Kagami-1/AudioMorph/Images/0.96-inch-OLED-display-1-1536x1536.jpg

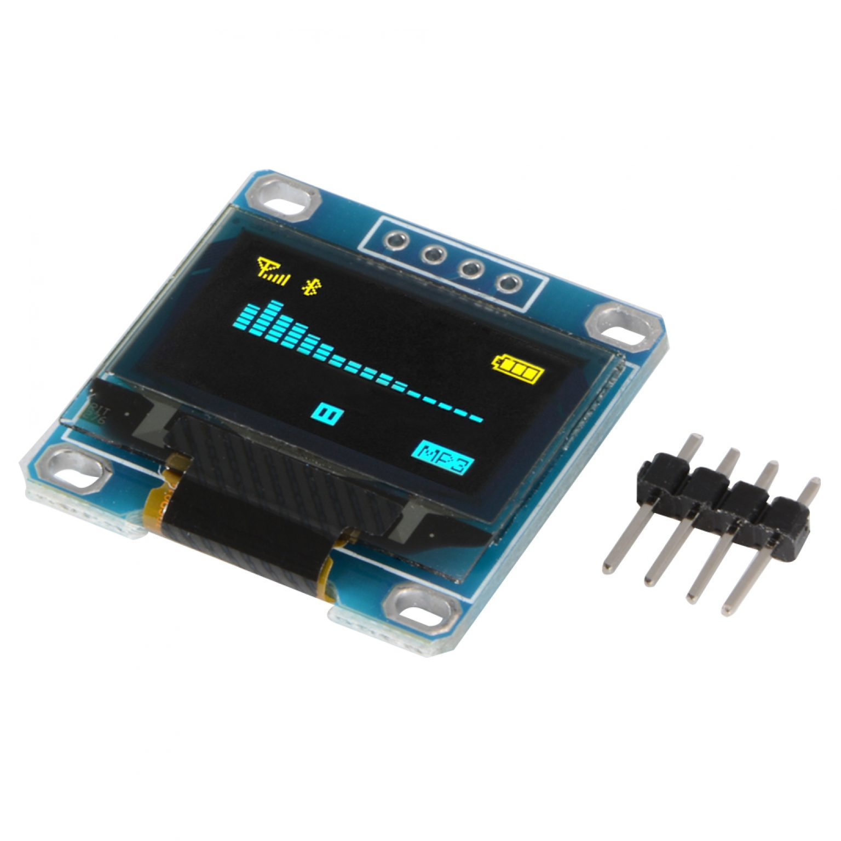
Images/0.96-inch-OLED-display-1-1536x1536.jpg
