Kagami-1/AudioMorph/Images/467a1c06-c707-43bd-9dd6-f2bde50086d6_1.46be4bbbeaa72e5d1ce6fceb8eb4fa7a.webp

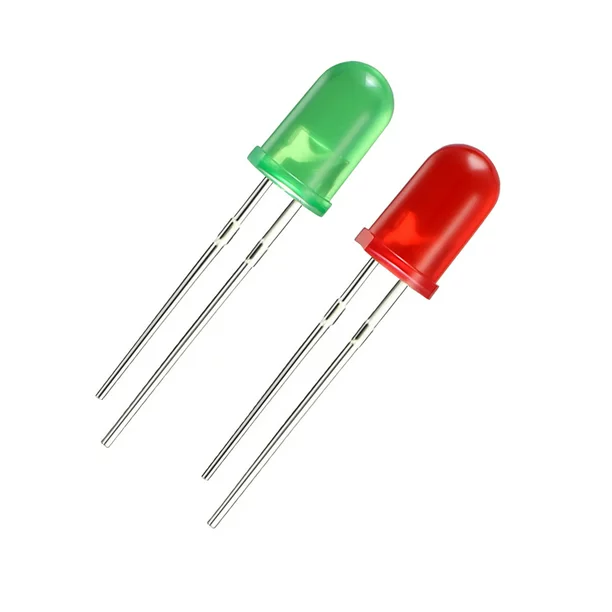
Images/467a1c06-c707-43bd-9dd6-f2bde50086d6_1.46be4bbbeaa72e5d1ce6fceb8eb4fa7a.webp
