Kagami-1/AudioMorph/Images/breadboard.jpg

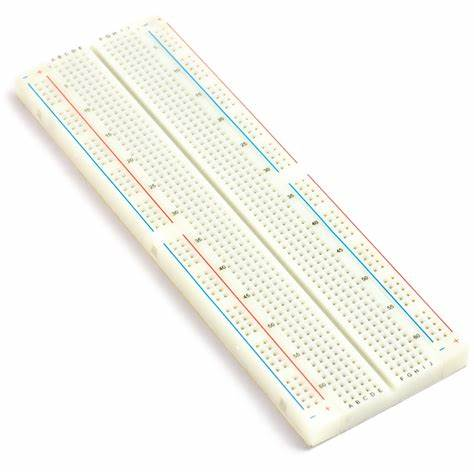
Images/breadboard.jpg
