Kagami-1/AudioMorph/Images/ezgif-1-566e2a0541.gif

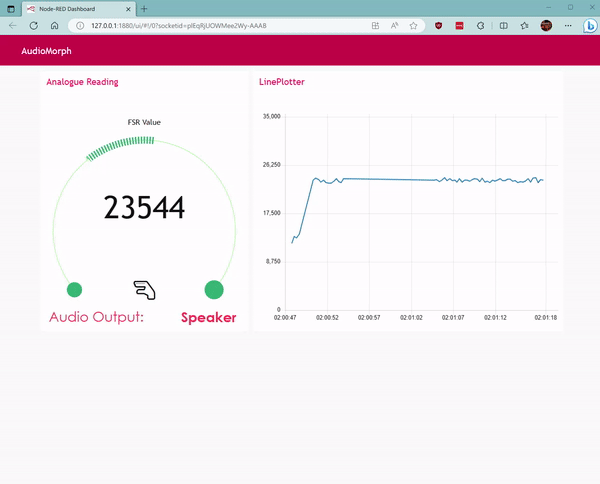
Images/ezgif-1-566e2a0541.gif
