Kagami-1/AudioMorph/Images/New folder/Screenshot 2023-07-06 210006.png

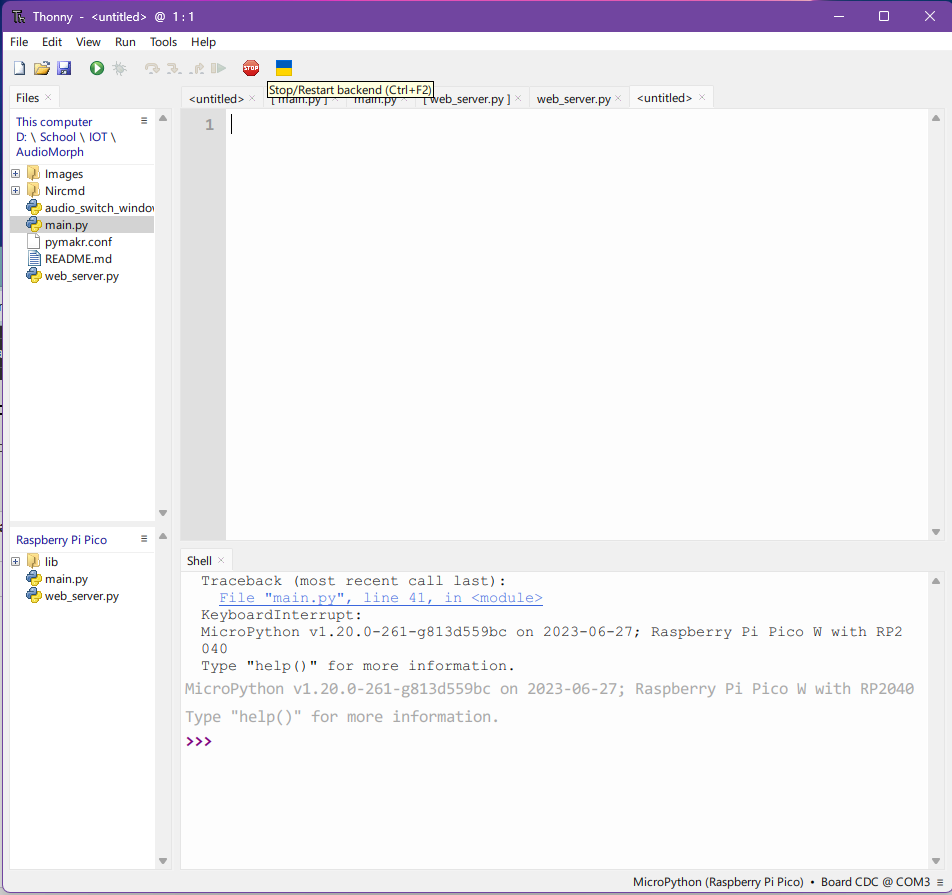
Images/New folder/Screenshot 2023-07-06 210006.png
