Kagami-1/AudioMorph/Images/photo_2023-07-06_21-38-20.jpg

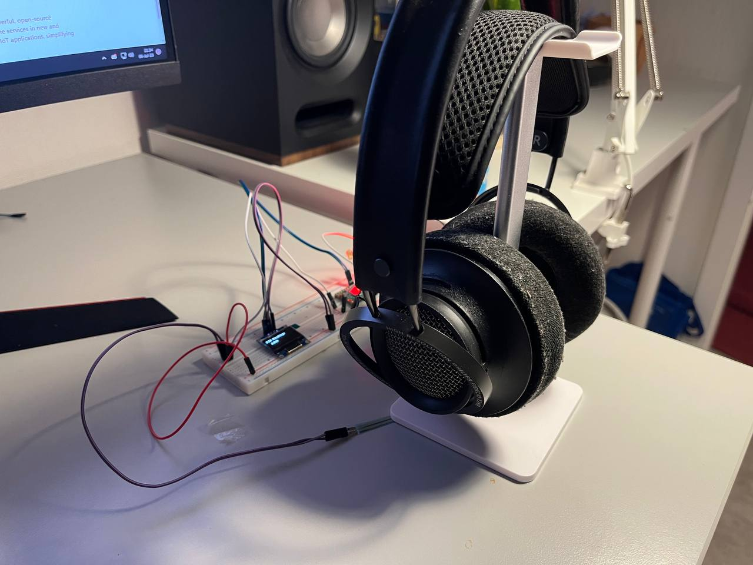
Images/photo_2023-07-06_21-38-20.jpg
