Kagami-1/AudioMorph/Images/pi pico WH.jpg

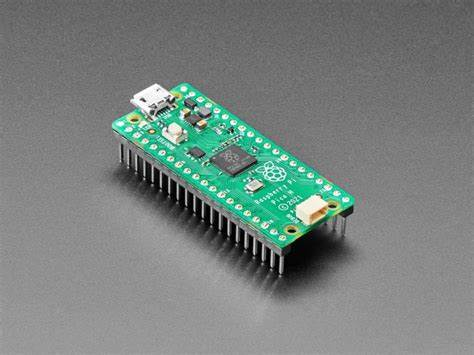
Images/pi pico WH.jpg
