Kagami-1/AudioMorph/Images/pico.jpg

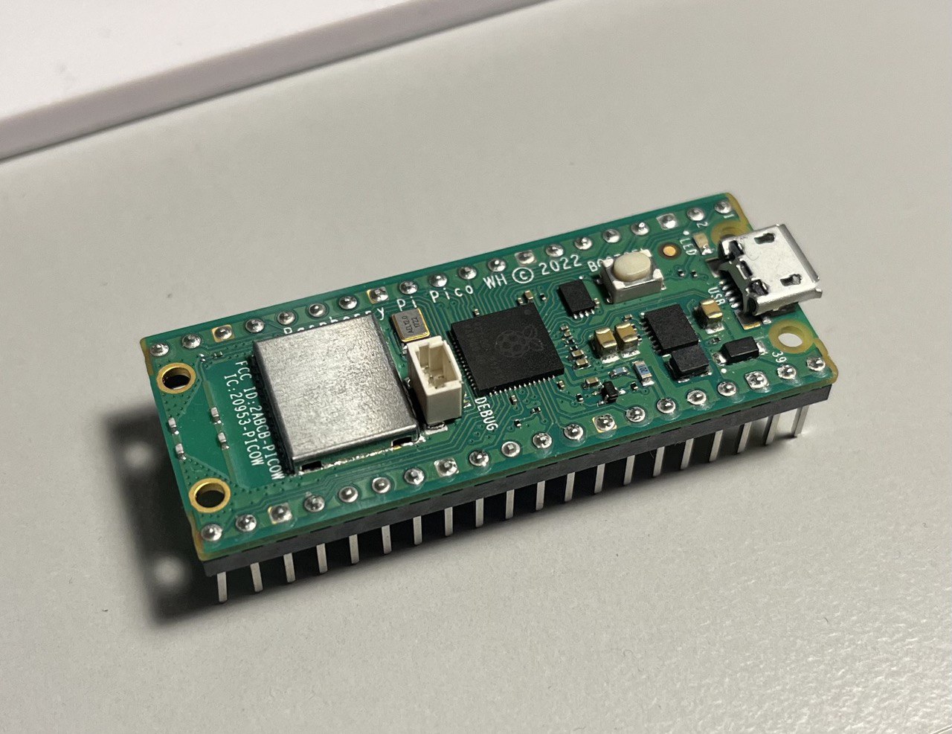
Images/pico.jpg
