Kagami-1/AudioMorph/Images/smart_headphone_stand with fsr_bb.jpg

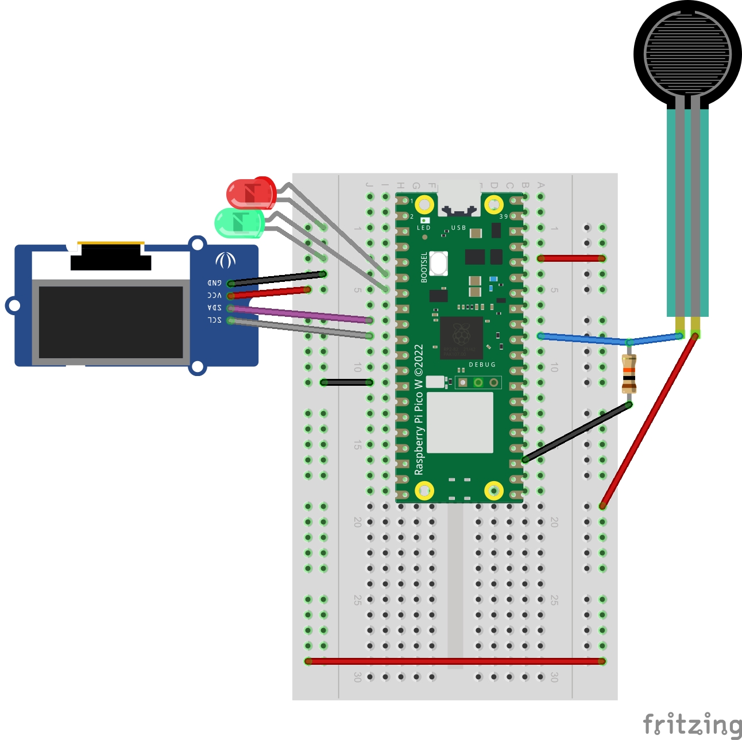
Images/smart_headphone_stand with fsr_bb.jpg
